HarrisonChe5188/Redstone-Circuit/connectors/lamppistonconnector.STL

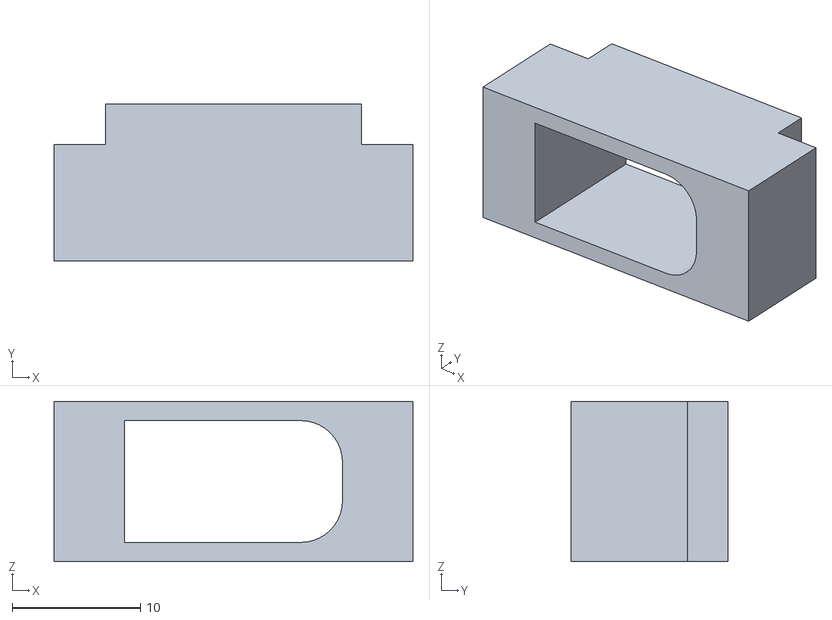
[picture p19: CAD file, 2025-03-19]
connectors/lamppistonconnector.STL
28.0 x 12.2 x 12.5
