HarrisonChe5188/Redstone-Circuit/lever/levercap.STL

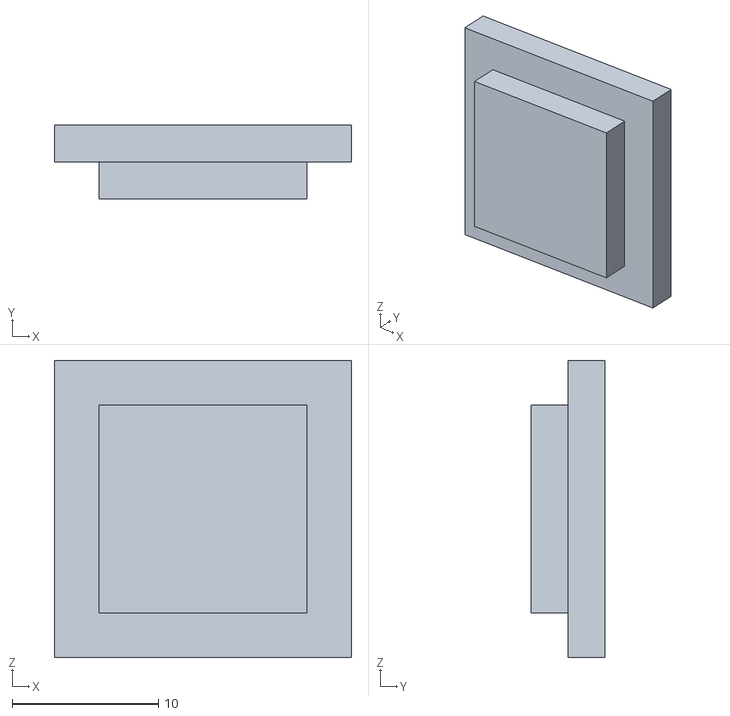
[picture p20: CAD file, 2025-03-19]
lever/levercap.STL
20.3 x 5.08 x 20.3
