HarrisonChe5188/Redstone-Circuit/piston/linkage.stl

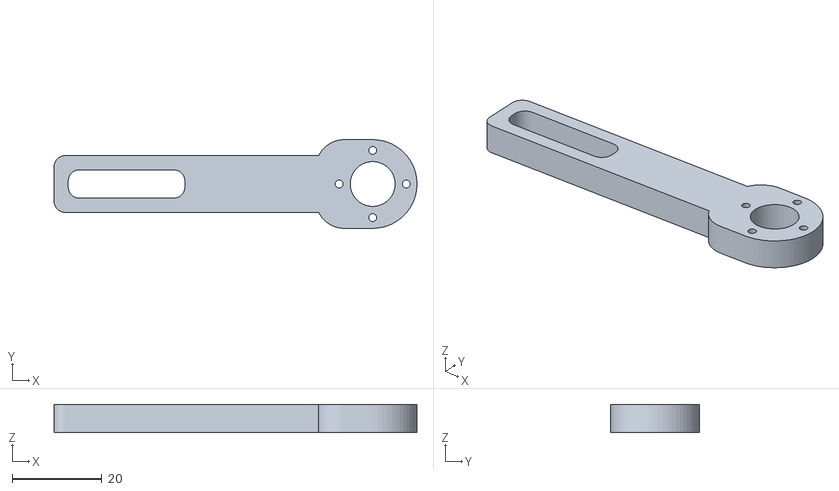
[picture p21: CAD file, 2025-03-19]
piston/linkage.stl
81.0 x 19.8 x 6.35
